dmitryshagin/led_driver_12v_1a/LT3791.asc

C1: cap; 22n
C2: cap; 22n
C3: cap; 470n
C4: cap; 4.7µ; V=25 Irms=8.64 Rser=0.0031053 Lser=0 mfg="KEMET" pn="C1206C475K3RAC" type="X7R"
C5: cap; .1µ
C6: cap; 0.1µ; V=50 Irms=728m Rser=0.14361 Lser=0 mfg="KEMET" pn="C0603C104K5RAC" type="X7R"
C7: cap; 0.1µ; V=50 Irms=728m Rser=0.14361 Lser=0 mfg="KEMET" pn="C0603C104K5RAC" type="X7R"
C8: cap; 4.7µ; V=25 Irms=8.64 Rser=0.0031053 Lser=0 mfg="KEMET" pn="C1206C475K3RAC" type="X7R"
C9: cap; 4.7µ; V=25 Irms=8.64 Rser=0.0031053 Lser=0 mfg="KEMET" pn="C1206C475K3RAC" type="X7R"
C10: cap; 4.7µ; V=25 Irms=8.64 Rser=0.0031053 Lser=0 mfg="KEMET" pn="C1206C475K3RAC" type="X7R"
C11: cap; 4.7µ; V=25 Irms=8.64 Rser=0.0031053 Lser=0 mfg="KEMET" pn="C1206C475K3RAC" type="X7R"
C12: cap; 4.7µ; V=25 Irms=8.64 Rser=0.0031053 Lser=0 mfg="KEMET" pn="C1206C475K3RAC" type="X7R"
C13: cap; 4.7µ; V=25 Irms=8.64 Rser=0.0031053 Lser=0 mfg="KEMET" pn="C1206C475K3RAC" type="X7R"
C14: cap; 4.7µ; V=25 Irms=8.64 Rser=0.0031053 Lser=0 mfg="KEMET" pn="C1206C475K3RAC" type="X7R"
C15: cap; 4.7µ; V=25 Irms=8.64 Rser=0.0031053 Lser=0 mfg="KEMET" pn="C1206C475K3RAC" type="X7R"
D1: LED; LXK2-PW14; N=3
D2: diode; BAT46WJ
D3: diode; BAT46WJ
L1: ind; 4.7µ; Ipk=8 Rser=0.008 Rpar=5192 Cpar=10.1p mfg="Wurth Elektronik" pn="744771004 WE-PD 1260"
L2: ind; 1000n; Ipk=3.2 Rser=0.02 Rpar=1092 Cpar=0 mfg="Bourns, Inc." pn="SRR7045-1R0M"
Q1: nmos; BSZ0902NSI
Q2: nmos; BSZ0902NSI
Q3: nmos; BSZ0902NSI
Q4: nmos; BSZ0902NSI
Q5: nmos; BSZ0902NSI
R2: res; 300k
R3: res; 56.9k
R4: res; 50
R7: res; 86.6K
R8: res; 10m
R9: res; 1Meg
R10: res; 86.6K
R11: res; 50m
R14: res; 100K
R15: res; 56.9K
U1: LT3791
V1: voltage; 11.7; Rser=0.01
Named nets: 0, IN
.tran 7m steady startup
Note:
  If the simulation model is not found please update with the "Sync Release" command from the "Tools" menu.
  It remains the customer's responsibility to verify proper and reliable operation in the actual application.
  Component substitution and printed circuit board layout may significantly affect circuit performance or reliability.
  Contact your local sales representative for assistance. This circuit is distributed to customers only for use with LTC parts.
  Copyright © 2012 Linear Technology Inc. All rights reserved.
LT3791 - 60V 4-Switch Synchronous Buck-Boost LED Driver Controller
98% Efficient 50W Buck-Boost LED Driver
Input: 4.7V to 58V       Output: 25V LED @ 2A
